mi3nts/bikeSensor/resources/_bikeWaggle_01_FINAL.jpg

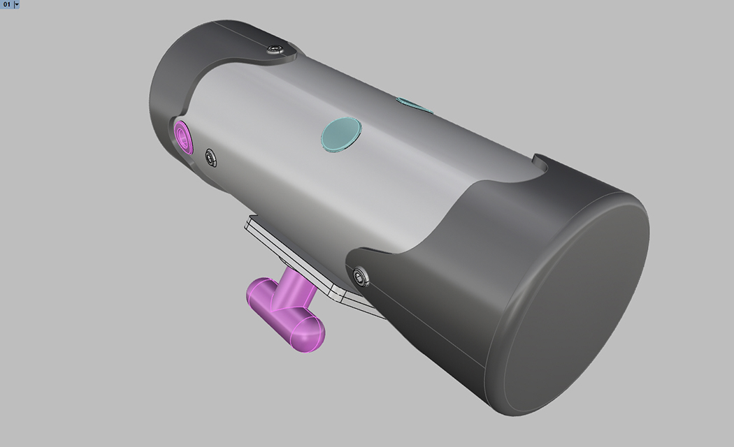
resources/_bikeWaggle_01_FINAL.jpg
