mi3nts/bikeSensor/resources/_bikeWaggle_05_FINAL.jpg

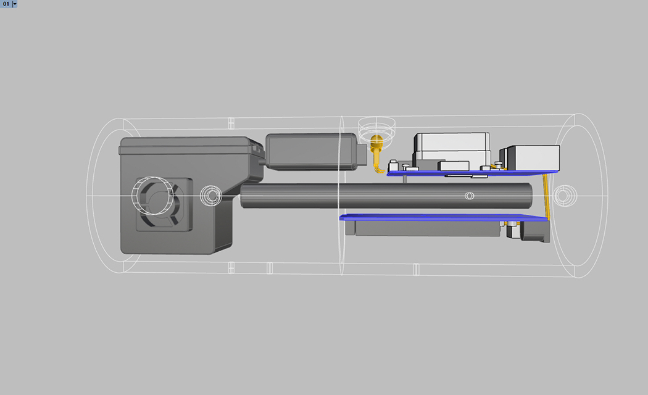
resources/_bikeWaggle_05_FINAL.jpg
