mi3nts/bikeSensor/resources/_bikeWaggle_08_FINAL.jpg

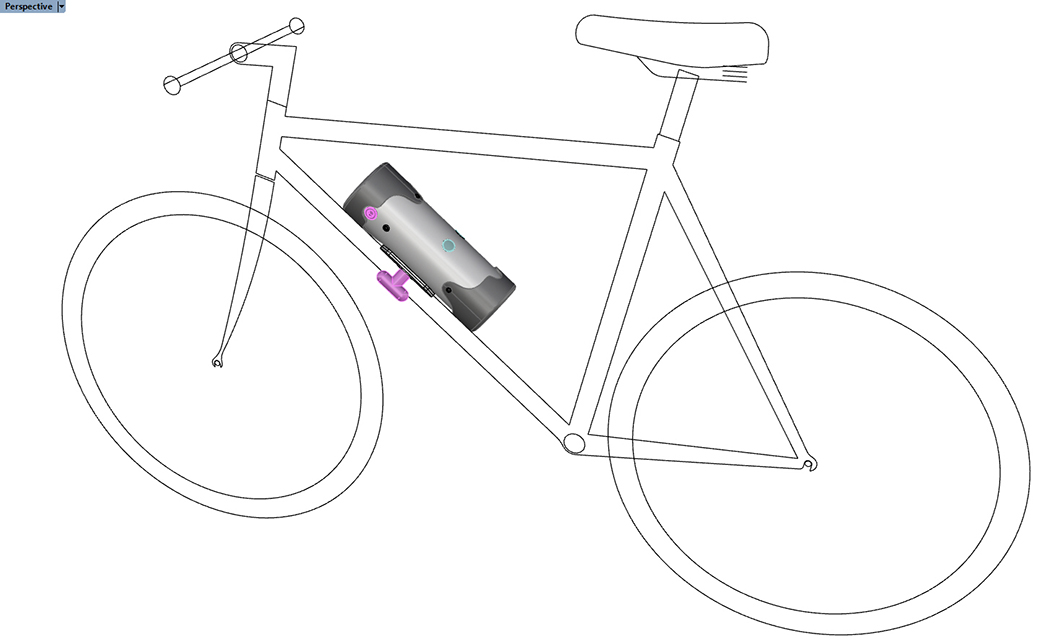
resources/_bikeWaggle_08_FINAL.jpg
