mi3nts/bikeSensor/resources/_bikeWaggle_09_FINAL.jpg

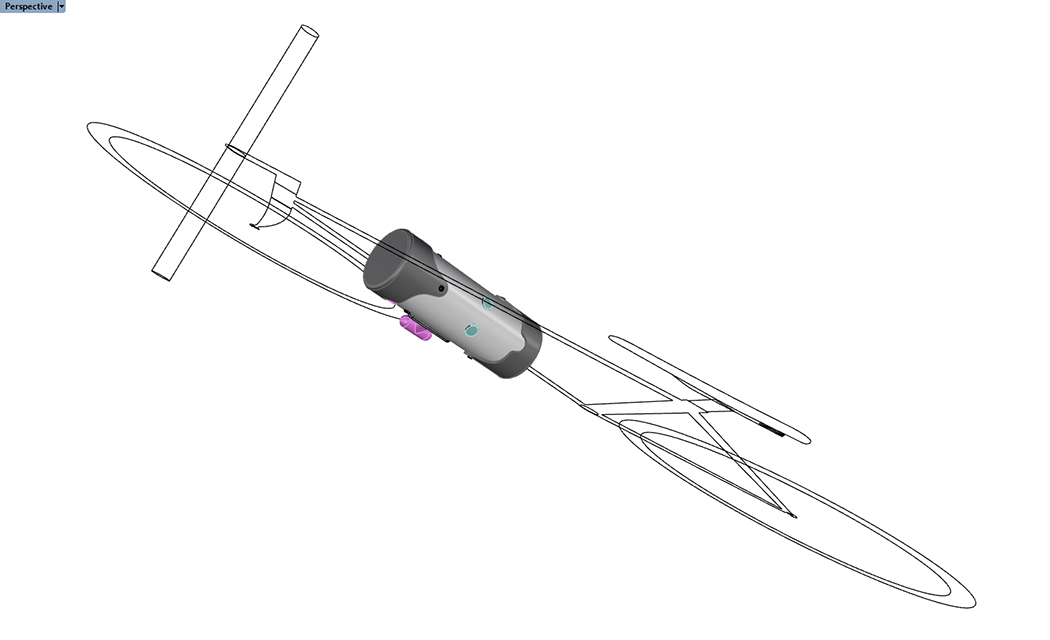
resources/_bikeWaggle_09_FINAL.jpg
