mi3nts/bikeSensor/resources/_bikeWaggle_11_FINAL.jpg

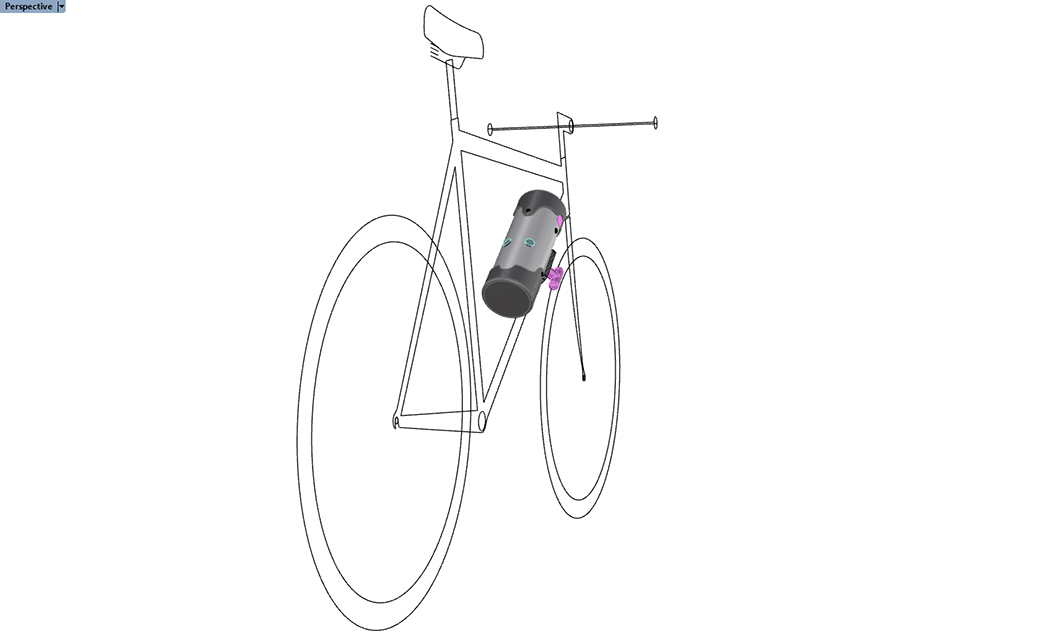
resources/_bikeWaggle_11_FINAL.jpg
